ab4421/SIoTSmartWaterBottle/AppFiles/AppScreenshots/DataViewWithAverage.jpg

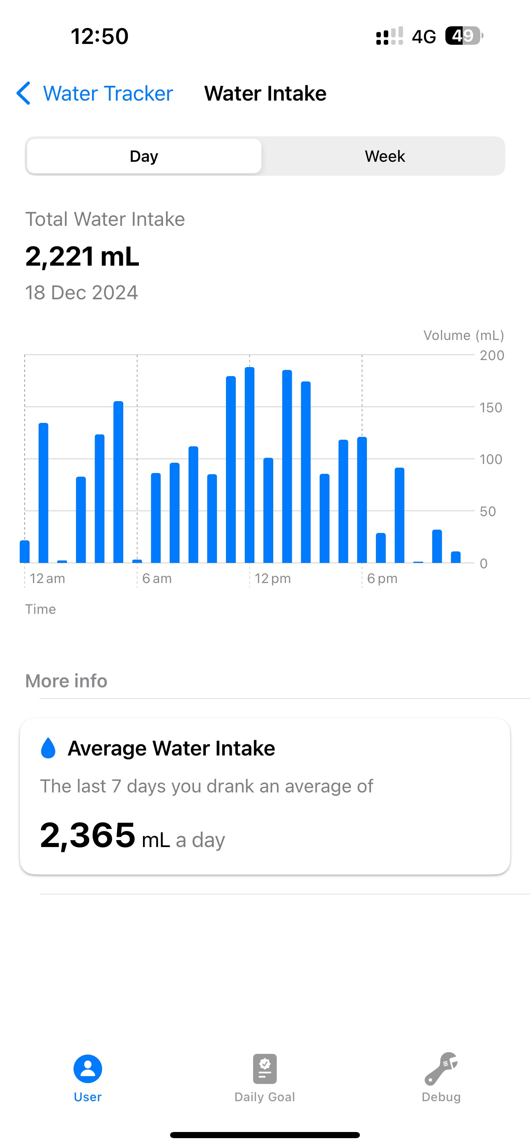
AppFiles/AppScreenshots/DataViewWithAverage.jpg
