ab4421/SIoTSmartWaterBottle/AppFiles/AppScreenshots/GoalAdjustSheet.PNG

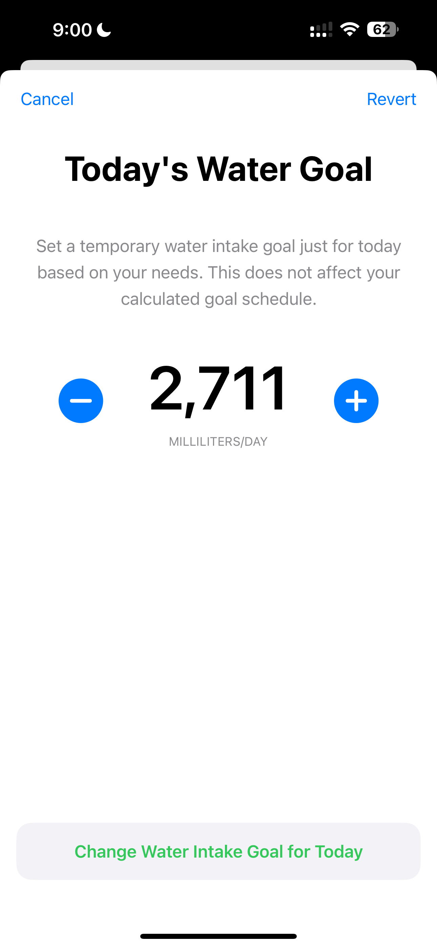
AppFiles/AppScreenshots/GoalAdjustSheet.PNG
