ab4421/SIoTSmartWaterBottle/AppFiles/AppScreenshots/ResetIntakeAlert.PNG

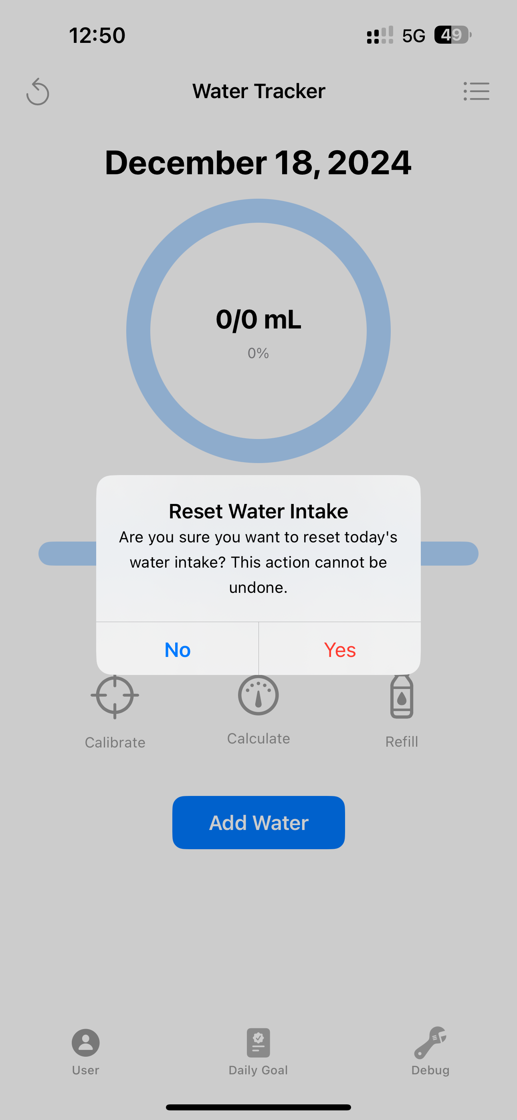
AppFiles/AppScreenshots/ResetIntakeAlert.PNG
