ab4421/SIoTSmartWaterBottle/RawSensorDataPlots/imu_plot_1468521.png

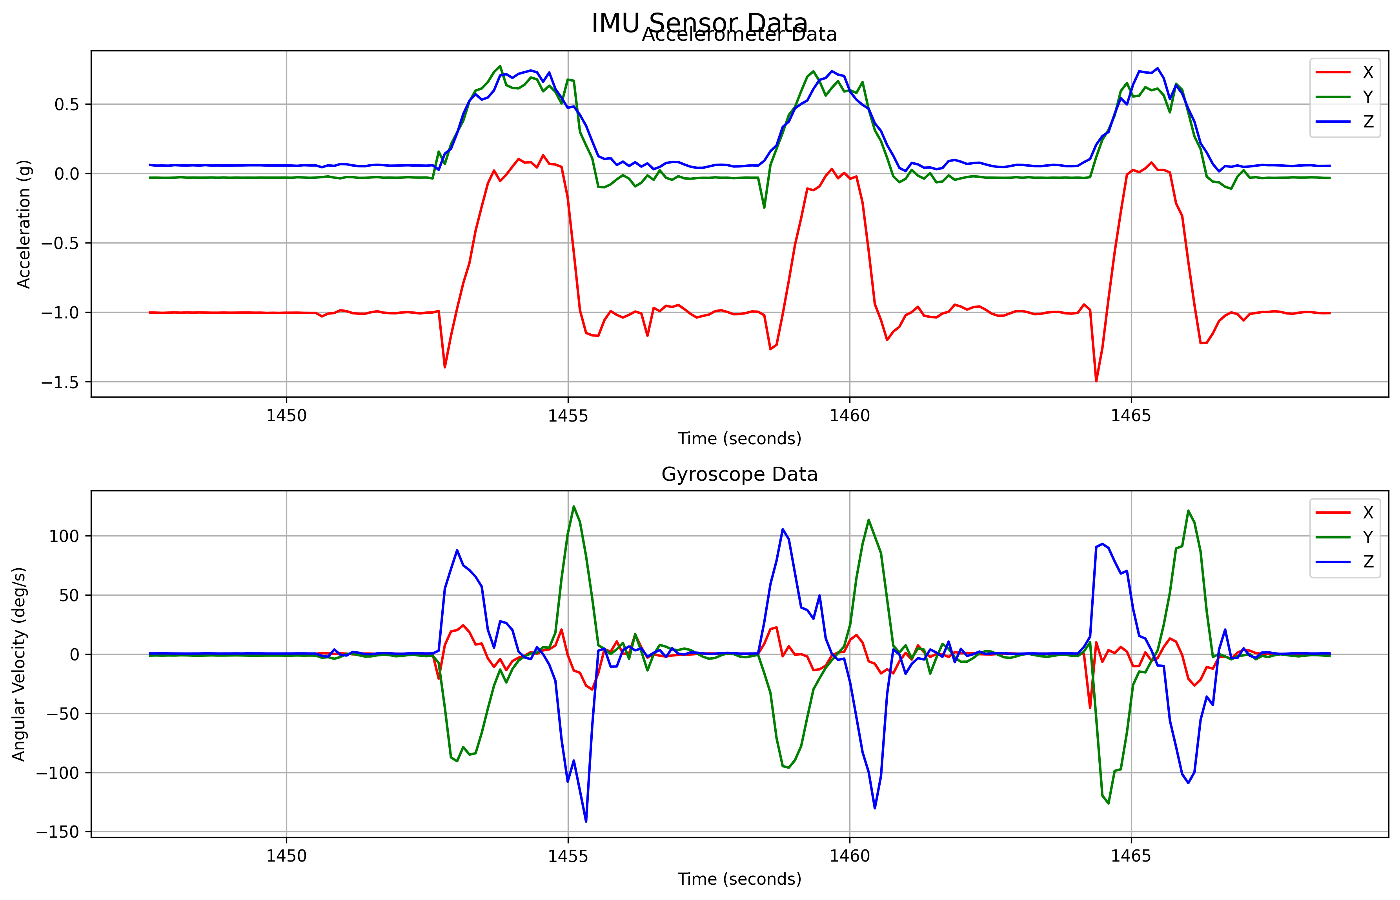
RawSensorDataPlots/imu_plot_1468521.png
