ab4421/SIoTSmartWaterBottle/RawSensorDataPlots/scale_plot_20241217_173914.png

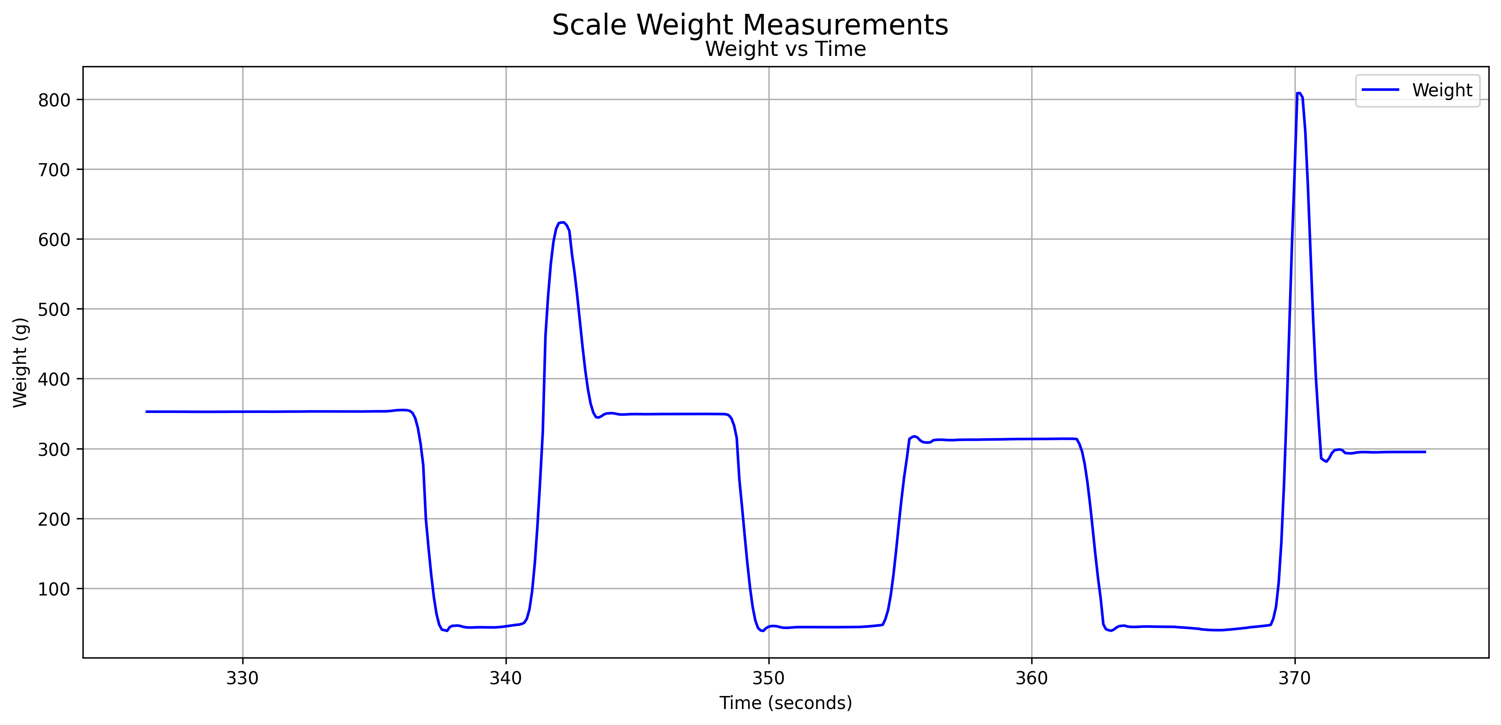
RawSensorDataPlots/scale_plot_20241217_173914.png
