ab4421/SIoTSmartWaterBottle/AppFiles/AppScreenshots/ManualWaterSheet.PNG

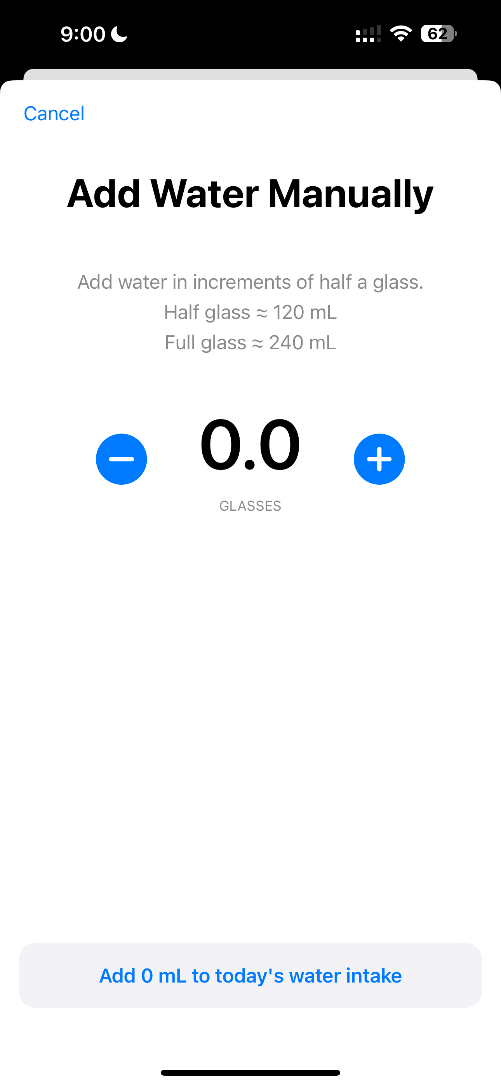
AppFiles/AppScreenshots/ManualWaterSheet.PNG
