ab4421/SIoTSmartWaterBottle/WiringDiagram.png

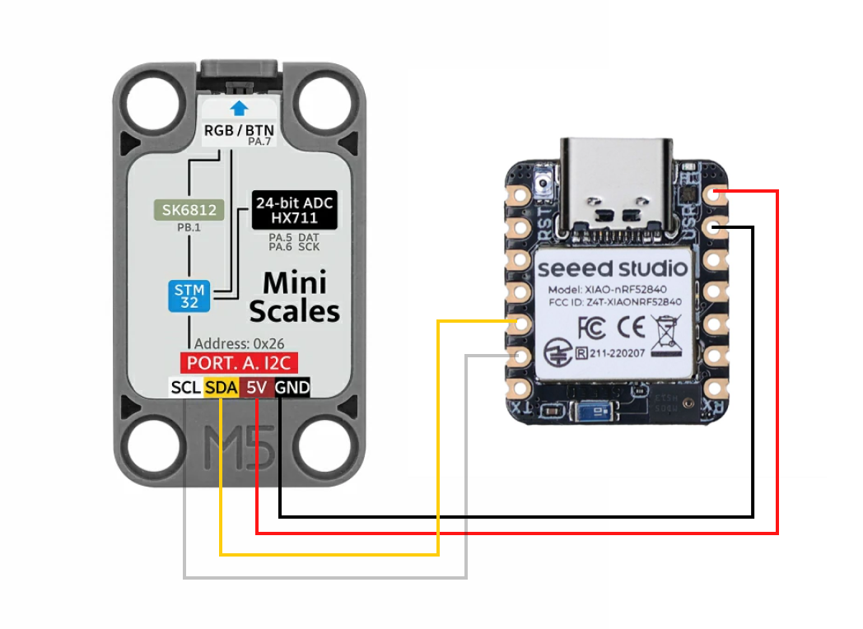
WiringDiagram.png
