ab4421/SIoTSmartWaterBottle/AppFiles/AppScreenshots/DebugView.PNG

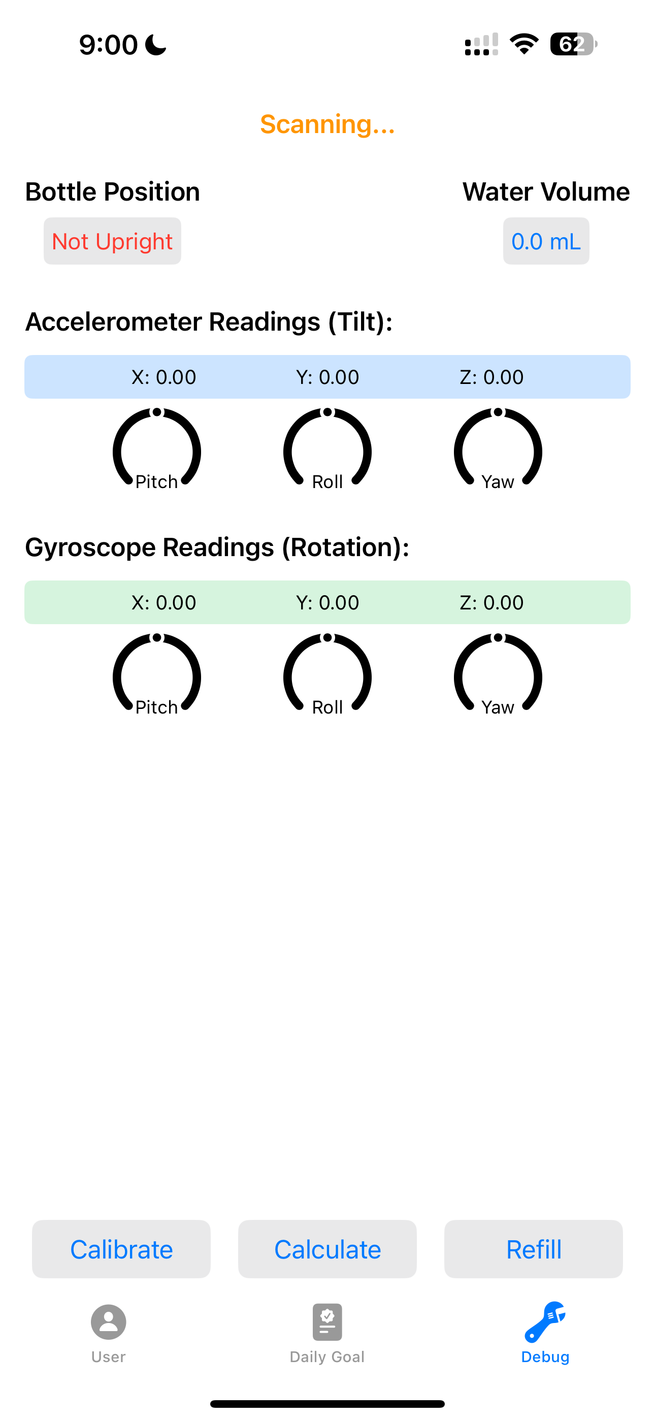
AppFiles/AppScreenshots/DebugView.PNG
